HaraldRieder/Matrix_to_MIDI/V3GrandPianoXXL.h

static midi::DataByte buff[20];

struct Sound {
  midi::DataByte bank;
  midi::DataByte prognum;
};

const struct Sound 
  GPViennaRock = { 0, 2 }, GPHamburgRock = { 0, 3 },
  GrandPianoVienna/*Bösendorfer*/ = { 0, 4 }, GrandPianoHamburg/*Steinway*/ = { 0, 5 }, 
  GPViennaLayeredPad = { 0, 16 }, GPHamburgLayeredPad = { 0, 17 }, 
  GPViennaLayeredStrings = { 0, 18 }, GPHamburgLayeredStrings = { 0, 19 },
  GPViennaDream = { 0, 20 }, GPHamburgDream = { 0, 21 },
  MK1DynoTremolo/*Fender Rhodes*/ = { 0, 31 }, MK1DynoLayeredPad = { 0, 32 }, MK1DynoLayeredFM = { 0, 33 }, MK1Tremolo = { 0, 37 }, MK1LayeredFM = { 0, 39 },
  A200 = { 0, 41 }, A200Tremolo1/*Wurlitzer*/ = { 0, 43 }, FMPianoLayeredMKS = { 0, 23 }, V3BellaLayeredCortales = { 0, 54 },
  Organ776555678fast = { 1, 1 }, Organ800000568fast = { 1, 3 }, Organ008530000fast = { 1, 5 }, Organ807800000slow = { 1, 8 },
  HammondFull = { 1, 20 },
  DigitalPad = { 2, 1 }, Brightness = { 2, 5 }, FairlySpace = { 2, 14 }, IceRain = { 2, 21 },  Ice = { 2, 45 }, 
  VPhrase = { 2, 47 }, M12Brass = { 2, 64 }, Brazza = { 2, 71 }, OBLeadBPF24 = { 2, 102 },
  Harpsichord = { 3, 47 }, HarpsichordOctave = { 3, 48 },
  GuitarNylon = { 3, 22 }, GuitarNylonSoft = { 3, 23 }, GuitarSteel = { 3, 26 }, GuitarSteelSoft = { 3, 27 },
  EGuitarClean = { 3, 43 }, EGuitarDistortion = { 3, 45 },
  HarpLong = { 3, 60 },
  UprJazzBassVel96 = { 3, 67 }, UprightJazzBass = { 3, 71 }, EBassUS1 = { 3, 79 }, EBassUS2 = { 3, 80 }, EBassPick = { 3, 82 }, EBassPickDark = { 3, 83 },
  EBassFretless = { 3, 84 }, SlapBass1 = { 3, 85 }, SlapBass2 = { 3, 86 },
  SynBass = { 2, 116 }, JBassSoft = { 3, 121 }, CSClassicBass = { 3, 122 }, MOBassENV = { 3, 124 },
  XBass1 = { 3, 125 }, XBass2 = { 3, 126 },
  Strings2Forte = { 4, 8 }, Strings3 = { 4, 13 }, 
  DiscoStringsLong = { 4, 16 }, StringsPWMA = { 4, 29 }, StringsM12D = { 4, 42 },
  ClassicChoirAahFilter = { 4, 65 },
  USTrumpetSection = { 5, 32 }, USTrumpTrombSection = { 5, 42 },
  PopDrumKit = { 4, 120 }, JazzDrumKit = { 4, 121 }, OrchestraPercussion = { 4, 122 }, VoiceKit = { 4, 123 },
  NoSound = { 0, 127 };

// my favourite non-split and accompanying sounds
const Sound * sounds[] = {
  & GrandPianoHamburg, & GrandPianoVienna, 
  & GPViennaLayeredPad, & GPHamburgLayeredPad,
  & GPHamburgLayeredStrings, & GPViennaLayeredStrings,
  & Harpsichord, & HarpsichordOctave,
  & MK1DynoTremolo, & MK1DynoLayeredPad,
  & MK1Tremolo, & MK1LayeredFM,
  & A200Tremolo1, & FMPianoLayeredMKS,
  & V3BellaLayeredCortales, & NoSound, // reserved
  & GuitarNylon, & GuitarNylonSoft,
  & GuitarSteel, & GuitarSteelSoft,
  & HarpLong, & NoSound, // reserved
  & PopDrumKit, & JazzDrumKit,
  & OrchestraPercussion, & VoiceKit
};
const int n_sounds = sizeof(sounds) / sizeof (sounds[0]);

const Sound * bass_sounds[] = {
  & UprightJazzBass, & EBassUS1, 
  & EBassUS2, & EBassPick, 
  & EBassPickDark, & EBassFretless,
  & SlapBass1, & SlapBass2,
  & SynBass, & JBassSoft, 
  & CSClassicBass, & MOBassENV,
  & XBass1, & XBass2
};
const int n_bass_sounds = sizeof(bass_sounds) / sizeof (bass_sounds[0]);

/** 
 * corresponds to 1 line of a V3 Control registration
 */
struct Preset {
  const Sound & sound;
  midi::DataByte volume; // difference from 100
  midi::DataByte coarsetune; // difference from 0 [semitones]
  midi::DataByte reverb; // absolute
  midi::DataByte chorus; // abs. value
  midi::DataByte attack; // difference from 64
  midi::DataByte decay;  // difference from 64
  midi::DataByte release; // difference from 64
  midi::DataByte cutoff; // difference from 64
//  midi::DataByte finetune; // difference from 0 [cent]
//  midi::DataByte pan; // difference from center position
//  boolean mono; // 1 note only if true
};

/**
 * corresponds to a V3 Control registration
 */
struct Registration {
  const midi::DataByte reverbType, effectType;
  const Preset left, right1, right2;
};

const struct Registration  
  AintNoSunshine = { 1,2, {UprightJazzBass,15,0,2,0,0,0,10/*release*/}, {StringsPWMA,0,0,15}, {MK1Tremolo,-10,0,10,33} },
  AllCriedOut = { 1,0, {SynBass,0,0,4,0,0,0,10/*release*/}, {Ice,0,0,15}, {FairlySpace,-10,0,15} },
  Bedingungslos = { 1,0, {EBassPickDark,15,0,2,0,0,0,10/*release*/}, {VPhrase,0,0,15}, {GPViennaLayeredStrings,-10,0,15} },
  CatchTheRainbow = { 1,0, {EBassUS2,15,0,2,0,0,0,10/*release*/}, {ClassicChoirAahFilter,0,0,15}, {GPHamburgLayeredPad,-10,0,15} },
  DontPayTheFerryman = { 1,0, {EBassUS2,15,0,2,0,0,0,10/*release*/}, {Brazza,0,0,15}, {GPHamburgLayeredPad,-10,0,15} },
  DontYouNeed = { 1,0, {EBassFretless,15,0,8,0,0,0,18/*release*/}, {Brightness,0,0,15}, {GuitarSteelSoft,-41,0,15} },
  IchWillKeineSchokolade = { 1,0, {UprJazzBassVel96,15,0,2,0,0,0,10/*release*/}, {USTrumpetSection,0,0,15}, {Organ800000568fast,-55,0,15} }, 
  LetItRain = { 1,2, {EBassUS2,15,0,2,0,0,0,10/*release*/}, {HammondFull,0,0,15}, {MK1DynoTremolo,-10,0,10,33} },
  MeAndBobbyMcGee = { 1,0, {EBassUS1,15,0,2,0,0,0,10/*release*/}, {Organ776555678fast,0,0,15}, {Organ807800000slow,-41,0,15} }, 
  NieGenug = { 1,0, {EBassUS1,15,0,2}, {EGuitarDistortion,0,-12/*transpose*/,25,74,0,0,8/*release*/}, {EGuitarClean,-41,0,15,120/*chorus*/,0,0,17,-10/*cutoff*/} }, 
  RideLikeTheWind = { 1,0, {MOBassENV,0,0,2,0,0,0,4/*release*/}, {M12Brass, 0,0,15}, {GPHamburgDream, -10,0,15} }, 
  RollingInTheDeep = { 1,0, {EBassPickDark,15,0,2,0,0,0,10/*release*/}, {Strings3,0,-12/*transpose*/,15}, {GPHamburgRock, -10,0,15} }, 
  SummerDreaming = { 1,0, {EBassFretless,15,0,2,0,0,10/*decay*/}, {Organ008530000fast,0,0,15}, {A200,-10,0,15,16/*chorus*/} }, 
  ThatOleDevilCalledLove = { 1,0, {UprightJazzBass,15,0,2}, {USTrumpTrombSection,0,0,15}, {GrandPianoHamburg,-10,0,15} },
  ThisIsTheLife = { 1,2, {EBassFretless,15,0,2,0,0,18/*decay*/}, {Strings2Forte,0,0,15}, {GuitarSteel,-41,0,20,87/*chorus*/,0,0,8/*release*/} },
  ThisMasquerade = { 1,0, {UprightJazzBass,15,0,2,0,0,0,10/*release*/}, {Strings3,0,0,15}, {GrandPianoHamburg,-10,0,15} },
  UnderneathYourClothes = { 1,0, {EBassFretless,15,0,2,0,0,18/*decay*/}, {DigitalPad,0,12,15,0,0,8/*decay*/}, {StringsM12D,-41,0,15} },
  AintNobody = { 5,1, {SynBass,7,0,2,0,0,18/*decay*/}, {OBLeadBPF24,27,0,29}, {MK1DynoLayeredFM,-32,0,15,20} };

const Registration * registrations[] = {
  & AintNoSunshine, & AllCriedOut,
  & Bedingungslos,
  & CatchTheRainbow,
  & DontPayTheFerryman, & DontYouNeed,
  & LetItRain,
  & IchWillKeineSchokolade,
  & MeAndBobbyMcGee,
  & NieGenug,
  & RideLikeTheWind, & RollingInTheDeep,
  & SummerDreaming,
  & ThatOleDevilCalledLove, & ThisIsTheLife, & ThisMasquerade,
  & UnderneathYourClothes,
  & AintNobody
};

const int n_registrations = sizeof(registrations) / sizeof (registrations[0]);

enum GlobalNRPN {
  MainEQLowGain = 0x08, 
  MainEQLowMidGain = 0x09, 
  MainEQHighMidGain = 0x0A, 
  MainEQHighGain = 0x0B, 
  AuxEQLowGain = 0x12, 
  AuxEQLowMidGain = 0x13, 
  AuxEQHighMidGain = 0x14, 
  AuxEQHighGain = 0x15
};

void sendGlobalNRPN(GlobalNRPN nrpn, byte value,
                    midi::MidiInterface<midi::SerialMIDI<HardwareSerial>> & interface) {
  buff[0] = 0xB0; // channel always 0 here
  buff[1] = 0x63;
  buff[2] = 0x37;
  buff[3] = 0x62;
  buff[4] = nrpn;
  buff[5] = 0x06;
  buff[6] = value;
  interface.sendSysEx(7, buff);
}

/**
 * Global setting, always sent on channel 0.
 */
void sendReverbType(midi::DataByte type, 
                    midi::MidiInterface<midi::SerialMIDI<HardwareSerial>> & interface) {
  buff[0] = 0xf0;
  buff[1] = 0x41;
  buff[2] = 0x00;
  buff[3] = 0x42;
  buff[4] = 0x12;
  buff[5] = 0x40;
  buff[6] = 0x01;
  buff[7] = 0x30;
  buff[8] = type;
  buff[9] = 0x00;
  buff[10] = 0xf7;
  interface.sendSysEx(11, buff);
}

/**
 * Global setting, always sent on channel 0.
 */
void sendEffectType(midi::DataByte type,
                    midi::MidiInterface<midi::SerialMIDI<HardwareSerial>> & interface) {
  buff[0] = 0xf0;
  buff[1] = 0x41;
  buff[2] = 0x00;
  buff[3] = 0x42;
  buff[4] = 0x12;
  buff[5] = 0x40;
  buff[6] = 0x01;
  buff[7] = 0x38;
  buff[8] = type;
  buff[9] = 0x00;
  buff[10] = 0xf7;
  interface.sendSysEx(11, buff);
}

void sendGMReset(midi::MidiInterface<midi::SerialMIDI<HardwareSerial>> & interface) {
  buff[0] = 0xf0;
  buff[1] = 0x7e;
  buff[2] = 0x7f;
  buff[3] = 0x09;
  buff[4] = 0x01;
  buff[5] = 0xf7;
  interface.sendSysEx(6, buff);
}

/**
 * After power-on the XXL EQs are not flat! Must be flattened explicitly.
 */
void flattenEQs(midi::MidiInterface<midi::SerialMIDI<HardwareSerial>> & interface) {
  sendGlobalNRPN(MainEQLowGain, MIDI_CONTROLLER_MEAN, interface);
  sendGlobalNRPN(MainEQLowMidGain, MIDI_CONTROLLER_MEAN, interface);
  sendGlobalNRPN(MainEQHighMidGain, MIDI_CONTROLLER_MEAN, interface);
  sendGlobalNRPN(MainEQHighGain, MIDI_CONTROLLER_MEAN, interface);
  sendGlobalNRPN(AuxEQLowGain, MIDI_CONTROLLER_MEAN, interface);
  sendGlobalNRPN(AuxEQLowMidGain, MIDI_CONTROLLER_MEAN, interface);
  sendGlobalNRPN(AuxEQHighMidGain, MIDI_CONTROLLER_MEAN, interface);
  sendGlobalNRPN(AuxEQHighGain, MIDI_CONTROLLER_MEAN, interface);
}

/**
 * SYSEX F0H 7FH 7FH 04H 01H 00H II F7H 
 * Master volume (II=0 to 127, default 127)
 */
void sendMasterVolume(midi::DataByte volume,
                      midi::MidiInterface<midi::SerialMIDI<HardwareSerial>> & interface) {
  buff[0] = 0x7f;
  buff[1] = 0x7f;
  buff[2] = 0x04;
  buff[3] = 0x01;
  buff[4] = 0x00;
  buff[5] = volume;
  interface.sendSysEx(6, buff);
};

/**
 * Fine tune in cent BnH 65H 00H 64H 01H 06H vv
 * vv=00 -100 vv=40H 0 vv=7FH +100
 */
void sendFineTune(midi::DataByte value, 
                  midi::Channel channel, 
                  midi::MidiInterface<midi::SerialMIDI<HardwareSerial>> & interface) {
  buff[0] = 0xB0 + channel;
  buff[1] = 0x65;
  buff[2] = 0x00;
  buff[3] = 0x64;
  buff[4] = 0x01;
  buff[5] = 0x06;
  buff[6] = value;
  interface.sendSysEx(7, buff, true);                    
}

/**
 * Coarse tune in half tones BnH 65H 00H 64H 02H 06H vv
 * vv=00 -64 vv=40H 0 vv=7FH +64
 */
void sendCoarseTune(midi::DataByte value, 
                   midi::Channel channel, 
                   midi::MidiInterface<midi::SerialMIDI<HardwareSerial>> & interface) {
  buff[0] = 0xB0 + channel;
  buff[1] = 0x65;
  buff[2] = 0x00;
  buff[3] = 0x64;
  buff[4] = 0x02;
  buff[5] = 0x06;
  buff[6] = value;
  interface.sendSysEx(7, buff, true);                    
}

void sendSound(const Sound * sound, 
               midi::Channel channel, 
               midi::MidiInterface<midi::SerialMIDI<HardwareSerial>> & interface) {
  flattenEQs(interface);
  interface.sendControlChange(midi::BankSelect, sound->bank, channel); // only MSB necessary for V3 Sound Grand Piano XXL
  interface.sendProgramChange(sound->prognum, channel);
  interface.sendControlChange(0x77, 0, channel); // reset all NRPNs
};

void sendPreset(const Preset * preset, 
                midi::Channel channel, 
                midi::MidiInterface<midi::SerialMIDI<HardwareSerial>> & interface) {
  sendSound(&preset->sound, channel, interface);
  interface.sendControlChange(0x77, 0, channel); // reset all NRPNs
  interface.sendControlChange(midi::ChannelVolume, MIDI_CONTROLLER_MAX & (preset->volume + 100), channel);
  interface.sendControlChange(midi::ExpressionController, MIDI_CONTROLLER_MAX, channel); // reset expression value
  sendCoarseTune(MIDI_CONTROLLER_MAX & (preset->coarsetune + 64), channel, interface);
  interface.sendControlChange(midi::Effects1, MIDI_CONTROLLER_MAX & preset->reverb, channel);
  interface.sendControlChange(midi::Effects3, MIDI_CONTROLLER_MAX & preset->chorus, channel);
  interface.sendControlChange(midi::SoundController4, MIDI_CONTROLLER_MAX & (preset->attack + 64), channel);
  interface.sendControlChange(midi::SoundController6, MIDI_CONTROLLER_MAX & (preset->decay + 64), channel);
  interface.sendControlChange(midi::SoundController3, MIDI_CONTROLLER_MAX & (preset->release + 64), channel);
  interface.sendControlChange(midi::SoundController5, MIDI_CONTROLLER_MAX & (preset->cutoff + 64), channel);
};

void sendRegistration(const Registration * registration, 
                 midi::Channel base_channel,
                 midi::MidiInterface<midi::SerialMIDI<HardwareSerial>> & interface) {
  sendGMReset(interface);
  flattenEQs(interface);
  sendReverbType(&registration->reverbType, interface);
  sendEffectType(&registration->effectType, interface);
  sendPreset(&registration->left  , base_channel    , interface);                 
  sendPreset(&registration->right1, base_channel + 1, interface);                 
  sendPreset(&registration->right2, base_channel + 2, interface);
  sendFineTune(0x38, base_channel    , interface);
  sendFineTune(0x40, base_channel + 1, interface);
  sendFineTune(0x42, base_channel + 2, interface);
};
